promoteclab/OverPCB/lcd2.h

//LCD Functions Developed by Madeco_Pronic


void Lcd_Port(char a)
{
	if(a & 1)
		D4 = 1;
	else
		D4 = 0;

	if(a & 2)
		D5 = 1;
	else
		D5 = 0;

	if(a & 4)
		D6 = 1;
	else
		D6 = 0;

	if(a & 8)
		D7 = 1;
	else
		D7 = 0;
}
void Lcd_Cmd(char a)
{
	RS = 0;             // => RS = 0
	Lcd_Port(a);
	EN  = 1;             // => E = 1
        __delay_ms(4);
        EN  = 0;             // => E = 0
}

Lcd_Clear()
{
	Lcd_Cmd(0);
	Lcd_Cmd(1);
}

void Lcd_Set_Cursor(char a, char b)
{
	char temp,z,y;
	if(a == 1)
	{
	  temp = 0x80 + b - 1;
		z = temp>>4;
		y = temp & 0x0F;
		Lcd_Cmd(z);
		Lcd_Cmd(y);
	}
	else if(a == 2)
	{
		temp = 0xC0 + b - 1;
		z = temp>>4;
		y = temp & 0x0F;
		Lcd_Cmd(z);
		Lcd_Cmd(y);
	}
}

void Lcd_Init()
{
  Lcd_Port(0x00);
   __delay_ms(20);
  Lcd_Cmd(0x03);
	__delay_ms(5);
  Lcd_Cmd(0x03);
	__delay_ms(11);
  Lcd_Cmd(0x03);
  /////////////////////////////////////////////////////
  Lcd_Cmd(0x02);
  Lcd_Cmd(0x02);
  Lcd_Cmd(0x08);
  Lcd_Cmd(0x00);
  Lcd_Cmd(0x0C);
  Lcd_Cmd(0x00);
  Lcd_Cmd(0x06);
}

void Lcd_Write_Char(char a)
{
   char temp,y;
   temp = a&0x0F;
   y = a&0xF0;
   RS = 1;             // => RS = 1
   Lcd_Port(y>>4);             //Data transfer
   EN = 1;
   __delay_us(40);
   EN = 0;
   Lcd_Port(temp);
   EN = 1;
   __delay_us(40);
   EN = 0;
}

void Lcd_Write_String(char *a)
{
	int i;
	for(i=0;a[i]!='\0';i++)
	   Lcd_Write_Char(a[i]);
}

void Lcd_Shift_Right()
{
	Lcd_Cmd(0x01);
	Lcd_Cmd(0x0C);
}

void Lcd_Shift_Left()
{
	Lcd_Cmd(0x01);
	Lcd_Cmd(0x08);
}

void Lcd_Num(uint8_t d)
{
    switch (d)
        {
            case 0:
                Lcd_Write_String("00");
                break;
            case 1:
                Lcd_Write_String("01");
                break;
            case 2:
                Lcd_Write_String("02");
                break;
            case 3:
                Lcd_Write_String("03");
                break;
            case 4:
                Lcd_Write_String("04");
                break;
            case 5:
                Lcd_Write_String("05");
                break;
            case 6:
                Lcd_Write_String("06");
                break;
            case 7:
                Lcd_Write_String("07");
               break;
            case 8:
                Lcd_Write_String("08");
                break;
            case 9:
                Lcd_Write_String("09");
                break;
            case 10:
                Lcd_Write_String("10");
               break;
            case 11:
                Lcd_Write_String("11");
                break;
            case 12:
                Lcd_Write_String("12");
                break;
            case 13:
                Lcd_Write_String("13");
                break;
            case 14:
                Lcd_Write_String("14");
                break;
            case 15:
                Lcd_Write_String("15");
                break;
            case 16:
                Lcd_Write_String("16");
                break;
            case 17:
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
                Lcd_Write_String("60");
                break;
            case 61:
                Lcd_Write_String("61");
                break;
            default:
                Lcd_Set_Cursor(1,1);
                Lcd_Write_String("ERROR EE33");
                    
            }
}
